crami/piTimeLapse/parts/ThumbScrewM4.stl

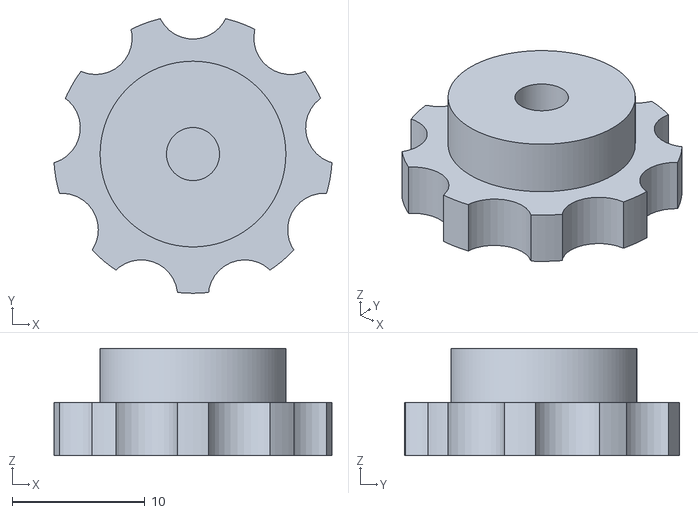
[picture p16: CAD file, 2015-01-30]
parts/ThumbScrewM4.stl
21.0 x 20.7 x 8.10
